htotoo/mayhem-mdk/src/portapack-external-module/main/ppi2c/pp_structures.hpp

#ifndef PP_STRUCTURES_HPP
#define PP_STRUCTURES_HPP

#include <cstdint>
#include <vector>

#define PP_API_VERSION 1
#define ESP_SLAVE_ADDR 0x51

enum class SupportedFeatures : uint64_t {
    FEAT_NONE = 0,
    FEAT_EXT_APP = 1 << 0,      // provides ext app
    FEAT_UART = 1 << 1,         // can handle uart commands
    FEAT_GPS = 1 << 2,          // provides gps info
    FEAT_ORIENTATION = 1 << 3,  // provides orientation info
    FEAT_ENVIRONMENT = 1 << 4,  // provides environment info (temp || hum || pressure)
    FEAT_LIGHT = 1 << 5,        // provides light info (lux)
    FEAT_DISPLAY = 1 << 6,      // has display to be used by pp
    FEAT_SHELL = 1 << 7,        // can handle shell commands (polling)
};

enum class Command : uint16_t {
    COMMAND_NONE = 0,

    // will respond with device_info
    COMMAND_INFO = 1,

    // will respond with info of application
    COMMAND_APP_INFO,

    // will respond with application data
    COMMAND_APP_TRANSFER,
    // Sensor specific commands
    COMMAND_GETFEATURE_MASK,
    COMMAND_GETFEAT_DATA_GPS,
    COMMAND_GETFEAT_DATA_ORIENTATION,
    COMMAND_GETFEAT_DATA_ENVIRONMENT,
    COMMAND_GETFEAT_DATA_LIGHT,
    // Shell specific communication
    COMMAND_SHELL_PPTOMOD_DATA,       // pp shell to esp. size not defined
    COMMAND_SHELL_MODTOPP_DATA_SIZE,  // how many bytes the esp has to send to pp's shell
    COMMAND_SHELL_MODTOPP_DATA,       // the actual bytes sent by esp. 1st byte's 1st bit is the "hasmore" flag, the remaining 7 bits are the size of the data. exactly 64 byte follows.

};

// data structures

typedef struct
{
    uint8_t hour;      /*!< Hour */
    uint8_t minute;    /*!< Minute */
    uint8_t second;    /*!< Second */
    uint16_t thousand; /*!< Thousand */
} ppgps_time_t;

typedef struct
{
    uint8_t day;   /*!< Day (start from 1) */
    uint8_t month; /*!< Month (start from 1) */
    uint16_t year; /*!< Year (start from 2000) */
} ppgps_date_t;

typedef struct
{
    float latitude;       /*!< Latitude (degrees) */
    float longitude;      /*!< Longitude (degrees) */
    float altitude;       /*!< Altitude (meters) */
    uint8_t sats_in_use;  /*!< Number of satellites in use */
    uint8_t sats_in_view; /*!< Number of satellites in view */
    float speed;          /*!< Ground speed, unit: m/s */
    ppgps_date_t date;    /*!< Fix date */
    ppgps_time_t tim;     /*!< time in UTC */
} ppgpssmall_t;

typedef struct
{
    float angle;
    float tilt;
} orientation_t;

typedef struct
{
    float temperature;
    float humidity;
    float pressure;
} environment_t;

typedef struct
{
    uint32_t api_version;
    uint32_t module_version;
    char module_name[20];
    uint32_t application_count;
} device_info;

enum app_location_t : uint32_t {
    UTILITIES = 0,
    RX,
    TX,
    DEBUG,
    HOME
};

typedef struct
{
    uint32_t header_version;
    uint8_t app_name[16];
    uint8_t bitmap_data[32];
    uint32_t icon_color;
    app_location_t menu_location;
    uint32_t binary_size;
} standalone_app_info;

typedef struct
{
    uint8_t* binary;
    uint32_t size;
} app_list_element_t;

typedef struct
{
    std::vector<uint8_t>* data;
} pp_command_data_t;

typedef void (*pp_i2c_command)(pp_command_data_t data);

typedef struct
{
    uint16_t command;
    pp_i2c_command got_command;
    pp_i2c_command send_command;
} pp_custom_command_list_element_t;

// callback typedefs

typedef void (*get_features_CB)(uint64_t& feat);
typedef void (*get_gps_data_CB)(ppgpssmall_t& gpsdata);
typedef void (*get_orientation_data_CB)(orientation_t& gpsdata);
typedef void (*get_environment_data_CB)(environment_t& envdata);
typedef void (*get_light_data_CB)(uint16_t& light);
typedef uint16_t (*get_shell_data_size_CB)();                                   // this wil be called when PP request MOD to send how many bytes it has in the outgoing (to shell) tx buffer. IRQ
typedef void (*got_shell_data_CB)(std::vector<uint8_t>& data);                  // this wil be called when got shell data from pp. IRQ
typedef void (*send_shell_data_CB)(std::vector<uint8_t>& data, bool& hasmore);  // this will be called when the module needs to send shell data to pp. Just pass the data, and set the hasmore. NO 0th byte set needed( that'll be set up inthe driver itself, just send your max 64 byte data). IRQ

#endif
