htotoo/mayhem-mdk/src/common/ui/bitmap.hpp

/*
 * Copyright (C) 2015 Jared Boone, ShareBrained Technology, Inc.
 * Copyright (C) 2016 Furrtek
 *
 * This file is part of PortaPack.
 *
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
 * You should have received a copy of the GNU General Public License
 * along with this program; see the file COPYING.  If not, write to
 * the Free Software Foundation, Inc., 51 Franklin Street,
 * Boston, MA 02110-1301, USA.
 */

// This file was generated by make_bitmap.py

#ifndef __BITMAP_HPP__
#define __BITMAP_HPP__

#include "ui.hpp"

namespace ui {

static constexpr uint8_t bitmap_arrow_left_data[] = {
    0x00,
    0x00,
    0x00,
    0x00,
    0x00,
    0x00,
    0x00,
    0x00,
    0x20,
    0x00,
    0x30,
    0x00,
    0x38,
    0x00,
    0xFC,
    0x7F,
    0xFE,
    0x7F,
    0xFC,
    0x7F,
    0x38,
    0x00,
    0x30,
    0x00,
    0x20,
    0x00,
    0x00,
    0x00,
    0x00,
    0x00,
    0x00,
    0x00,
};
static constexpr Bitmap bitmap_arrow_left{
    {16, 16},
    bitmap_arrow_left_data};

static constexpr uint8_t bitmap_arrow_right_data[] = {
    0x00,
    0x00,
    0x00,
    0x00,
    0x00,
    0x00,
    0x00,
    0x00,
    0x00,
    0x04,
    0x00,
    0x0C,
    0x00,
    0x1C,
    0xFE,
    0x3F,
    0xFE,
    0x7F,
    0xFE,
    0x3F,
    0x00,
    0x1C,
    0x00,
    0x0C,
    0x00,
    0x04,
    0x00,
    0x00,
    0x00,
    0x00,
    0x00,
    0x00,
};
static constexpr Bitmap bitmap_arrow_right{
    {16, 16},
    bitmap_arrow_right_data};

static constexpr uint8_t bitmap_bulb_ignore_data[] = {
    0x00,
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
    0x00,
    0x00,
    0x00,
    0x00,
    0x00,
    0x22,
    0xC7,
    0x8B,
    0x9E,
    0x0F,
    0x00,
    0x00,
    0x00,
    0x00,
    0x00,
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
};
static constexpr Bitmap bitmap_titlebar_image{
    {80, 16},
    bitmap_titlebar_image_data};

} /* namespace ui */

#endif /*__BITMAP_HPP__*/
